watterott/HDMI-Adapter/software/HDMI-Display/edid.cpp

#include "Arduino.h"
#include "HDMI-Display.h"

const uint8_t PROGMEM EDID::edid_unknown[EDID_SIZE] =
{
  0xFF,0xFF,0xFF,0xFF,0xFF,0xFF,0xFF,0xFF,0xFF,0xFF,0xFF,0xFF,0xFF,0xFF,0xFF,0xFF,
  0xFF,0xFF,0xFF,0xFF,0xFF,0xFF,0xFF,0xFF,0xFF,0xFF,0xFF,0xFF,0xFF,0xFF,0xFF,0xFF,
  0xFF,0xFF,0xFF,0xFF,0xFF,0xFF,0xFF,0xFF,0xFF,0xFF,0xFF,0xFF,0xFF,0xFF,0xFF,0xFF,
  0xFF,0xFF,0xFF,0xFF,0xFF,0xFF,0xFF,0xFF,0xFF,0xFF,0xFF,0xFF,0xFF,0xFF,0xFF,0xFF,
  0xFF,0xFF,0xFF,0xFF,0xFF,0xFF,0xFF,0xFF,0xFF,0xFF,0xFF,0xFF,0xFF,0xFF,0xFF,0xFF,
  0xFF,0xFF,0xFF,0xFF,0xFF,0xFF,0xFF,0xFF,0xFF,0xFF,0xFF,0xFF,0xFF,0xFF,0xFF,0xFF,
  0xFF,0xFF,0xFF,0xFF,0xFF,0xFF,0xFF,0xFF,0xFF,0xFF,0xFF,0xFF,0xFF,0xFF,0xFF,0xFF,
  0xFF,0xFF,0xFF,0xFF,0xFF,0xFF,0xFF,0xFF,0xFF,0xFF,0xFF,0xFF,0xFF,0xFF,0xFF,0xFF
};

const uint8_t PROGMEM EDID::edid_480x272[EDID_SIZE] =
{
  0x00,0xFF,0xFF,0xFF,0xFF,0xFF,0xFF,0x00,0x5C,0x34,0x01,0x00,0x01,0x00,0x00,0x00,
  0x01,0x19,0x01,0x03,0x81,0x00,0x00,0x00,0x0A,0x00,0x00,0x00,0x00,0x00,0x00,0x00,
  0x00,0x00,0x00,0x00,0x00,0x00,0x01,0x01,0x01,0x01,0x01,0x01,0x01,0x01,0x01,0x01,
  0x01,0x01,0x01,0x01,0x01,0x01,0xC4,0x09,0xE0,0x33,0x10,0x10,0x14,0x10,0x08,0x05,
  0x4A,0x00,0xE0,0x10,0x11,0x00,0x00,0x18,0x00,0x00,0x00,0xFC,0x00,0x48,0x44,0x4D,
  0x49,0x20,0x44,0x49,0x53,0x50,0x4C,0x41,0x59,0x0A,0x00,0x00,0x00,0x10,0x00,0x01,
  0x00,0x0A,0x00,0x0A,0x00,0x0A,0x0A,0x0A,0x0A,0x0A,0x20,0x0A,0x00,0x00,0x00,0x10,
  0x00,0x00,0x00,0x00,0x00,0x00,0x00,0x00,0x00,0x00,0x00,0x00,0x00,0x00,0x00,0x38
};

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
  {
    uint8_t b, d;

    #if USE_WATCHDOG > 0
      wdt_reset();
    #endif

    if(addr < length)
    {
      if(fromProgMem)
        b = pgm_read_byte(data + addr);
      else
        b = data[addr];
    }
    else
    {
      b = 0xFF;
    }

    d = readByte((uint8_t)addr);

    if(b != d)
    {
      #if DEBUG > 0
        Serial.print(F("EDID: verification failed at 0x"));
        Serial.println(addr, HEX);
      #endif
      err = false;
      break;
    }
  }

  digitalWrite(LED_RED, LOW);

  return err;
}

bool EDID::writeEDID(uint8_t display)
{
  uint8_t *data;

  #if DEBUG > 0
    Serial.print(F("EDID: "));
    Serial.println(display);
  #endif

  data = (uint8_t*)edid_unknown;

       if(display == DISPLAY_480x272)
    data = (uint8_t*)edid_480x272;
  else if(display == DISPLAY_800x480)
    data = (uint8_t*)edid_800x480;
  else if(display == DISPLAY_800x480_720x480)
    data = (uint8_t*)edid_800x480_720x480;
  else if(display == DISPLAY_800x480HY)
    data = (uint8_t*)edid_800x480HY;
  else if(display == DISPLAY_1024x600)
    data = (uint8_t*)edid_1024x600;
  else if((settings.data.screenWidth == 480) && (settings.data.screenHeight == 272))
    data = (uint8_t*)edid_480x272;
  else if((settings.data.screenWidth == 800) && (settings.data.screenHeight == 480))
    data = (uint8_t*)edid_800x480;
  else if((settings.data.screenWidth == 1024) && (settings.data.screenHeight == 600))
    data = (uint8_t*)edid_1024x600;

  return writeData((uint8_t*)data, EDID_SIZE, true);
}

/*
bool EDID::writeFromRam(void) // test
{
  char test[] = "0123456789";
  return writeData((uint8_t*)test, sizeof(test), false);
}
*/
