watterott/HDMI-Adapter/software/HDMI-Display/mouse.cpp

/*
  Mouse.cpp

  Copyright (c) 2015, Arduino LLC
  Original code (pre-library): Copyright (c) 2011, Peter Barrett
  Absolute mouse coordinates added by Watterott electronic.

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
  You should have received a copy of the GNU Lesser General Public
  License along with this library; if not, write to the Free Software
  Foundation, Inc., 51 Franklin St, Fifth Floor, Boston, MA  02110-1301  USA
*/

#include "Arduino.h"
#include "HDMI-Display.h"

#if USE_HIDPROJECT == 0 || !defined(USE_HIDPROJECT)

#include "HID.h"

static const uint8_t _hidReportDescriptor[] PROGMEM =
{
  // Mouse absolute
  0x05, 0x01,                    // USAGE_PAGE (Generic Desktop)
  0x09, 0x02,                    // USAGE (Mouse)
  0xa1, 0x01,                    // COLLECTION (Application)
  0x09, 0x01,                    //   USAGE (Pointer)
  0xa1, 0x00,                    //   COLLECTION (Physical)
  0x85, 0x01,                    //     REPORT_ID (1)
  0x05, 0x09,                    //     USAGE_PAGE (Button)
  0x19, 0x01,                    //     USAGE_MINIMUM (Button 1)
  0x29, 0x03,                    //     USAGE_MAXIMUM (Button 3)
  0x15, 0x00,                    //     LOGICAL_MINIMUM (0)
  0x25, 0x01,                    //     LOGICAL_MAXIMUM (1)
  0x95, 0x03,                    //     REPORT_COUNT (3)
  0x75, 0x01,                    //     REPORT_SIZE (1)
  0x81, 0x02,                    //     INPUT (Data,Var,Abs)
  0x95, 0x01,                    //     REPORT_COUNT (1)
  0x75, 0x05,                    //     REPORT_SIZE (5)
  0x81, 0x03,                    //     INPUT (Cnst,Var,Abs)

  0x05, 0x01,                    //     USAGE_PAGE (Generic Desktop)
  0x09, 0x30,                    //     USAGE (X)
  0x09, 0x31,                    //     USAGE (Y)
  0x35, 0x00,                    //     PHYSICAL_MINIMUM (0)
  0x46, (TOUCHMAX&0xFF), ((TOUCHMAX>>8)&0xFF), //     PHYSICAL_MAXIMUM (4095, 0x0fff)
  0x15, 0x00,                    //     LOGICAL_MINIMUM (0)
  0x26, (TOUCHMAX&0xFF), ((TOUCHMAX>>8)&0xFF), //     LOGICAL_MAXIMUM (4095, 0x0fff)
  0x75, 0x10,                    //     REPORT_SIZE (16)
  0x95, 0x02,                    //     REPORT_COUNT (2)
  0x81, 0x02,                    //     INPUT (Data,Var,Abs)

  0x09, 0x38,                    //     USAGE (Wheel)
  0x35, 0x00,                    //     PHYSICAL_MINIMUM (0)
  0x45, 0x00,                    //     PHYSICAL_MAXIMUM (0)
  0x15, 0x81,                    //     LOGICAL_MINIMUM (-127)
  0x25, 0x7f,                    //     LOGICAL_MAXIMUM (127)
  0x75, 0x08,                    //     REPORT_SIZE (8)
  0x95, 0x01,                    //     REPORT_COUNT (1)
  0x81, 0x06,                    //     INPUT (Data,Var,Rel)

  0xc0,                          //   END_COLLECTION
  0xc0,                          // END_COLLECTION 
};

Mouse_::Mouse_(void) : _buttons(0), _x(0), _y(0)
{
  static HIDSubDescriptor node(_hidReportDescriptor, sizeof(_hidReportDescriptor));
  HID().AppendDescriptor(&node);
}

void Mouse_::begin(void) 
{
}

void Mouse_::end(void) 
{
}

void Mouse_::click(uint8_t b)
{
  _buttons = b;
  move(0,0,0);
  _buttons = 0;
  move(0,0,0);
}

void Mouse_::moveAbsolute(int x, int y, signed char wheel)
{
  uint8_t m[6];

  if(x < 0)
    x = 0;
  else if(x > TOUCHMAX)
    x = TOUCHMAX;
  _x = x;

  if(y < 0)
    y = 0;
  else if(y > TOUCHMAX)
    y = TOUCHMAX;
  _y = y;

  m[0] = _buttons;
  m[1] = (x & 0xFF); //LSB
  m[2] = ((x>>8) & 0xFF); //MSB
  m[3] = (y & 0xFF); //LSB
  m[4] = ((y>>8) & 0xFF); //MSB
  m[5] = wheel;
  HID().SendReport(1, m, sizeof(m));
}

void Mouse_::moveAbsolute(int x, int y, signed char wheel, unsigned char buttons)
{
  _buttons = buttons;
  moveAbsolute(x, y, wheel);
}

void Mouse_::move(signed char x, signed char y, signed char wheel)
{
  moveAbsolute((_x+x), (_y+y), wheel);
}

/*
void Mouse_::move(signed char x, signed char y, signed char wheel)
{
  uint8_t m[4];
  m[0] = _buttons;
  m[1] = x;
  m[2] = y;
  m[3] = wheel;
  HID().SendReport(1, m, sizeof(m));
}
*/

void Mouse_::buttons(uint8_t b)
{
  if(b != _buttons)
  {
    _buttons = b;
    move(0,0,0);
  }
}

void Mouse_::press(uint8_t b) 
{
  buttons(_buttons | b);
}

void Mouse_::release(uint8_t b)
{
  buttons(_buttons & ~b);
}

bool Mouse_::isPressed(uint8_t b)
{
  if((b & _buttons) > 0)
    return true;

  return false;
}

#endif //USE_HIDPROJECT == 0 || !defined(USE_HIDPROJECT)
