watterott/HDMI-Adapter/software/HDMI-Display/touchpanel_none.h

#ifndef TOUCHPANEL_NONE_H
#define TOUCHPANEL_NONE_H

class Touchpanel_None : public Touchpanel // no Touchpanel present - do nothing
{
  public:
    inline Touchpanel_None() {}
    inline void on() {}
    inline void off() {}
    inline void setup() {}
    inline void calibration() {}
    inline void loop() {}
};

#endif  //TOUCHPANEL_NONE_H
